chrumck/KnurLogger/3DPrinting/boomTip.stl

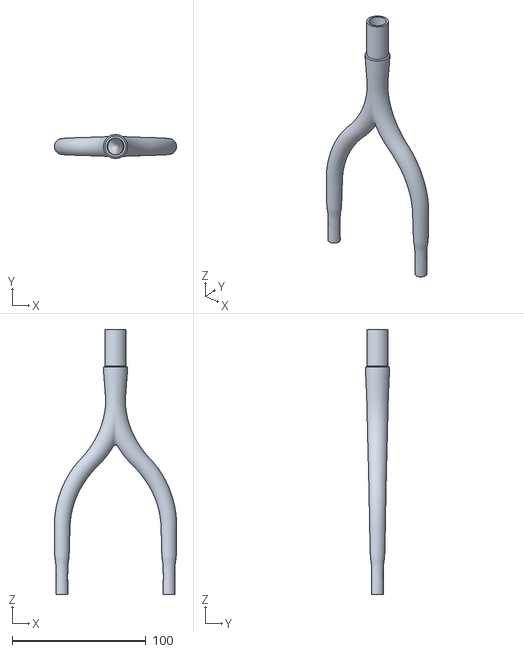
[picture p15: CAD file, 2026-09-19]
3DPrinting/boomTip.stl
91.4 x 18.0 x 198.0
