chrumck/KnurLogger/3DPrinting/cableTab.stl

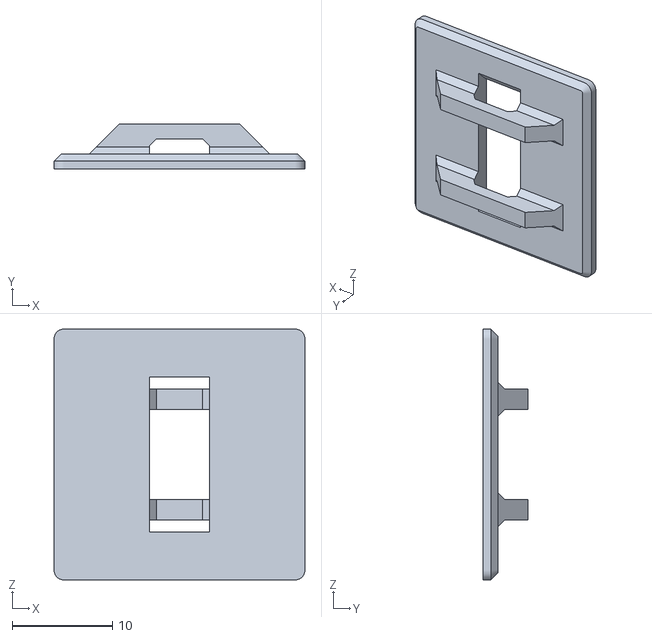
[picture p16: CAD file, 2026-09-10]
3DPrinting/cableTab.stl
25.0 x 4.50 x 25.0
