chrumck/KnurLogger/3DPrinting/cover.stl

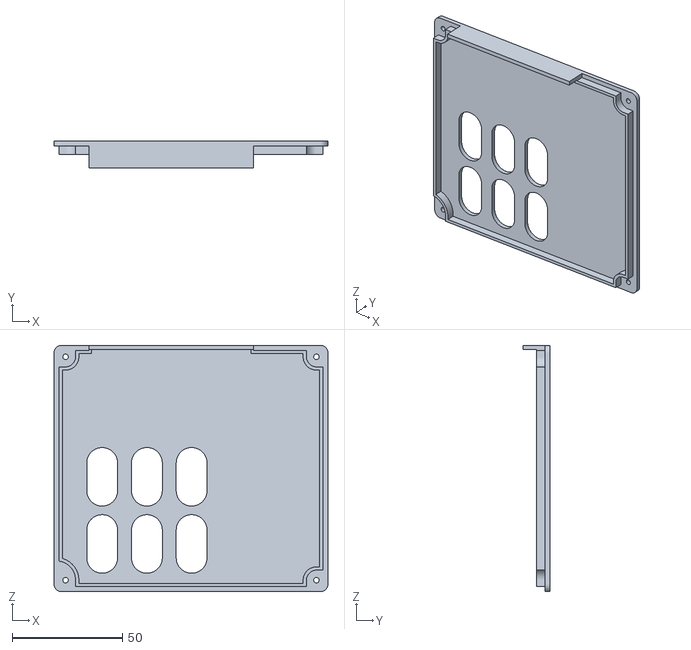
[picture p17: CAD file, 2026-09-09]
3DPrinting/cover.stl
124.5 x 12.2 x 112.0
