chrumck/KnurLogger/3DPrinting/pcbHolder.stl

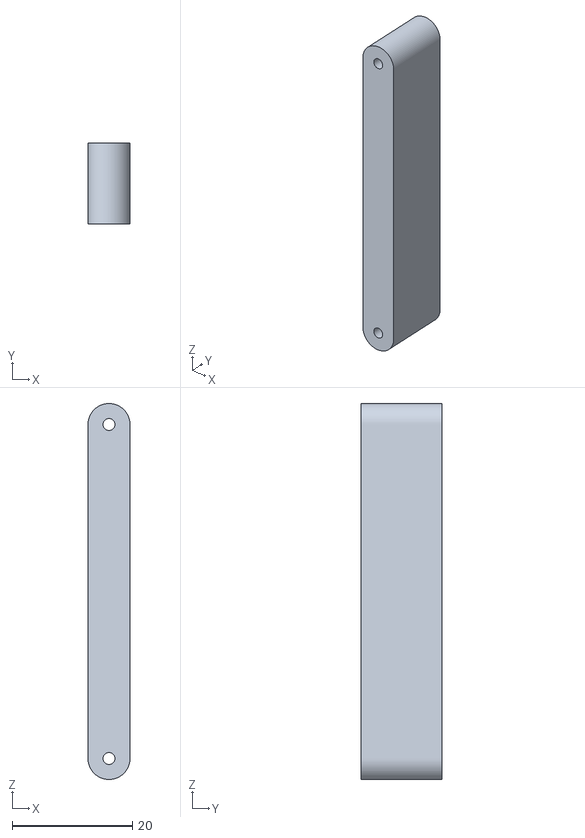
[picture p18: CAD file, 2026-09-09]
3DPrinting/pcbHolder.stl
7.00 x 13.5 x 62.6
