chrumck/KnurLogger/3DPrinting/case.stl

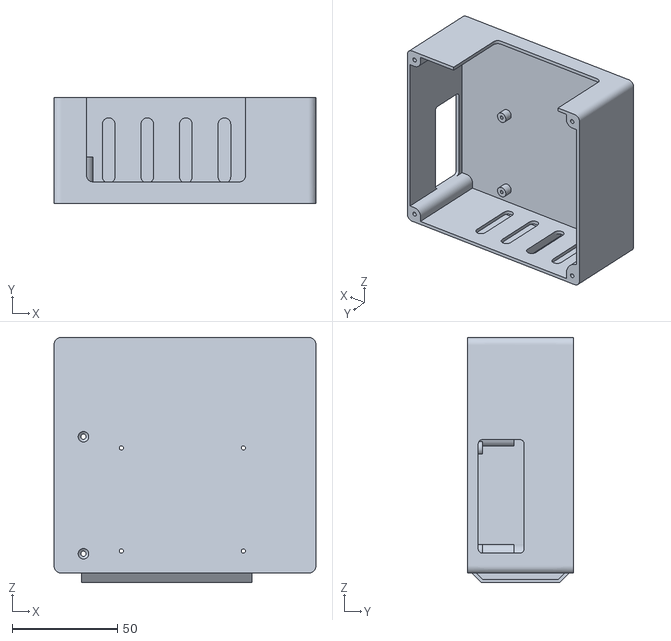
[picture p19: CAD file, 2026-09-09]
3DPrinting/case.stl
124.5 x 50.2 x 116.5
